Bambelweeny57/zxspectrum_issue3b/src/STPS/FERRANTI_ULA_6C001E-7.step

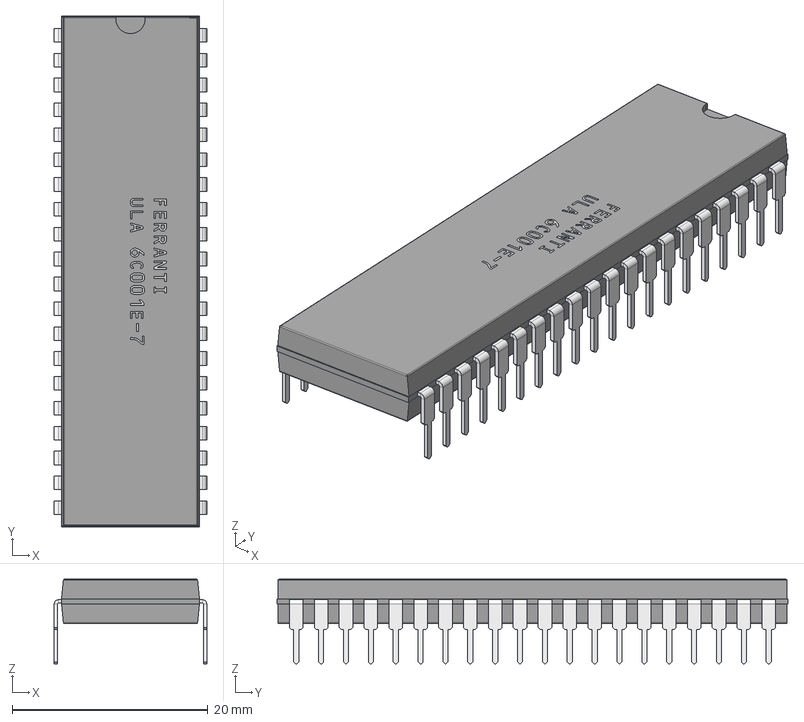
[picture p17: CAD file, 2026-09-03]
src/STPS/FERRANTI_ULA_6C001E-7.step
15.6 x 52.2 x 8.64 mm
Basic - DIP40 Wide v2
DIP Pin v2
DIP Pin v2(Mirror)
