Bambelweeny57/zxspectrum_issue3b/src/STPS/ROM HITACHI HN613128P.step

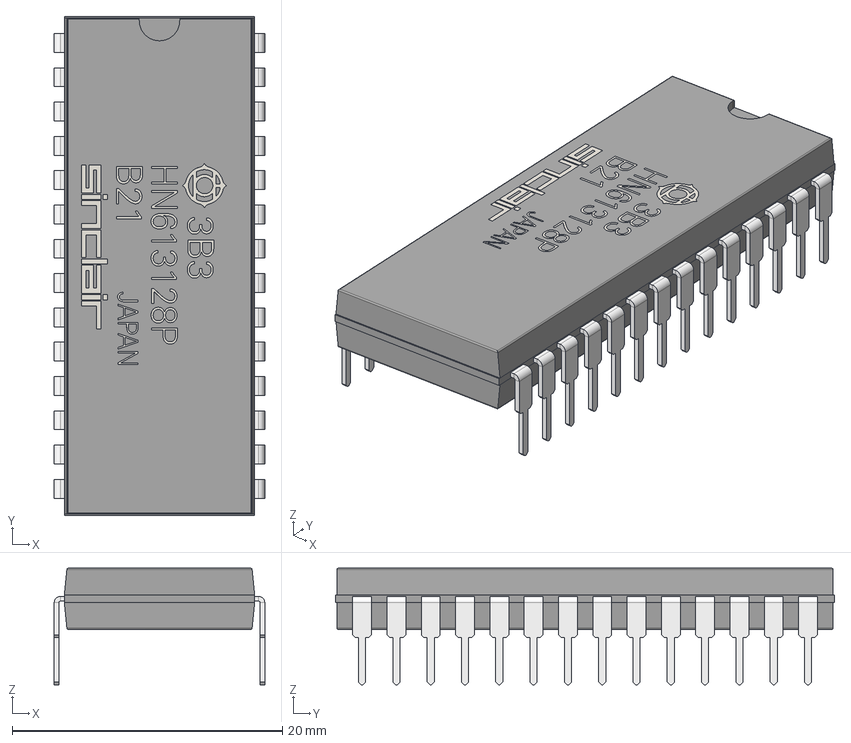
[picture p18: CAD file, 2026-09-03]
src/STPS/ROM HITACHI HN613128P.step
15.6 x 37.0 x 8.64 mm
Basic - DIP40 Wide v2
DIP Pin v2
DIP Pin v2(Mirror)
