Bambelweeny57/zxspectrum_issue3b/src/STPS/ZX Spectrum Speaker 40ohm.step

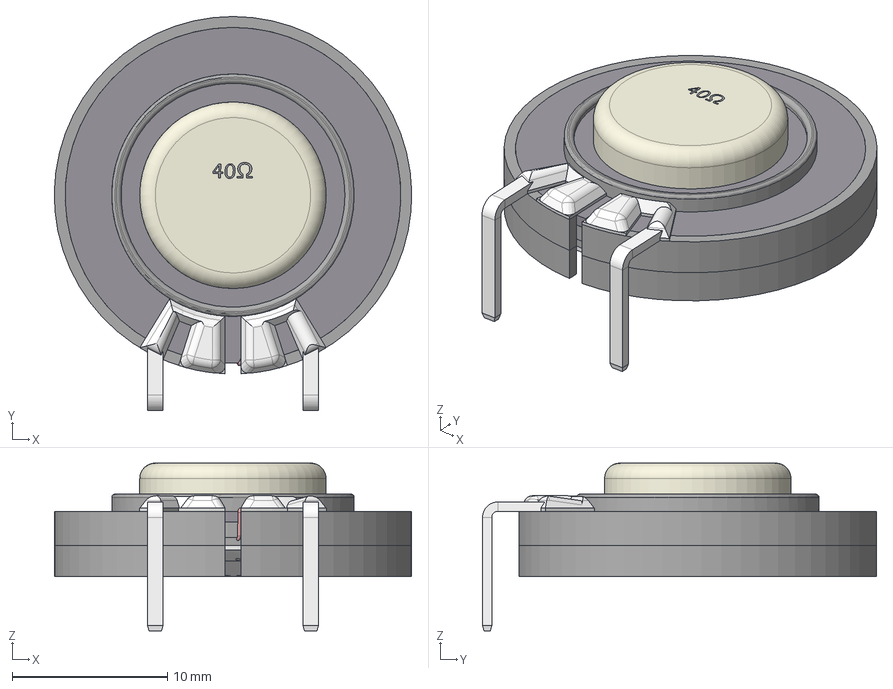
[picture p19: CAD file, 2026-09-01]
src/STPS/ZX Spectrum Speaker 40ohm.step
23.0 x 25.4 x 10.8 mm
Magnet
Plastic Cover
Board
CopperWire
Pins
