Bambelweeny57/zxspectrum_issue3b/src/STPS/COIL_L1.step

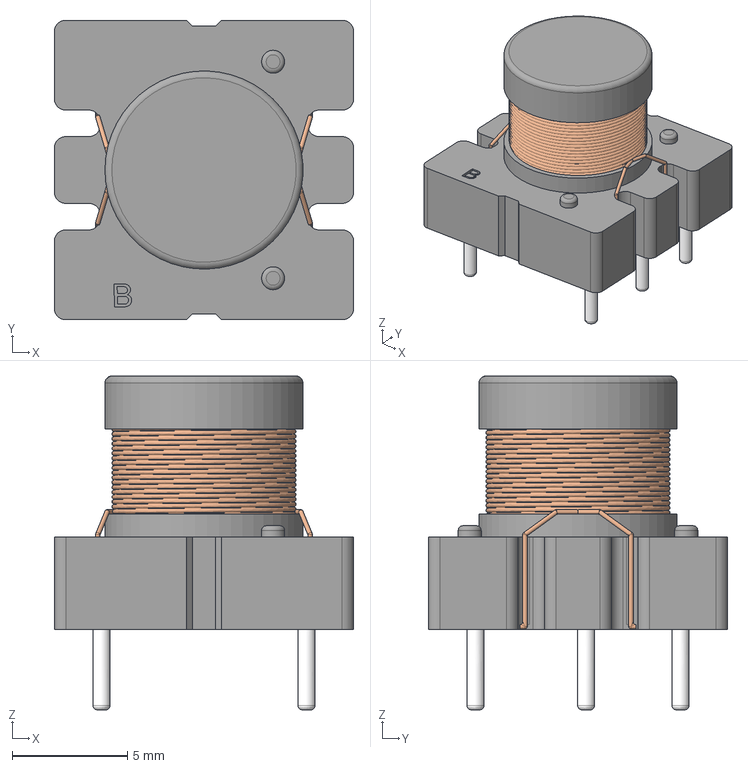
[picture p20: CAD file, 2026-09-01]
src/STPS/COIL_L1.step
13.0 x 13.0 x 14.5 mm
