Bambelweeny57/zxspectrum_issue3b/src/STPS/ZX Spectrum 48k Speaker.step

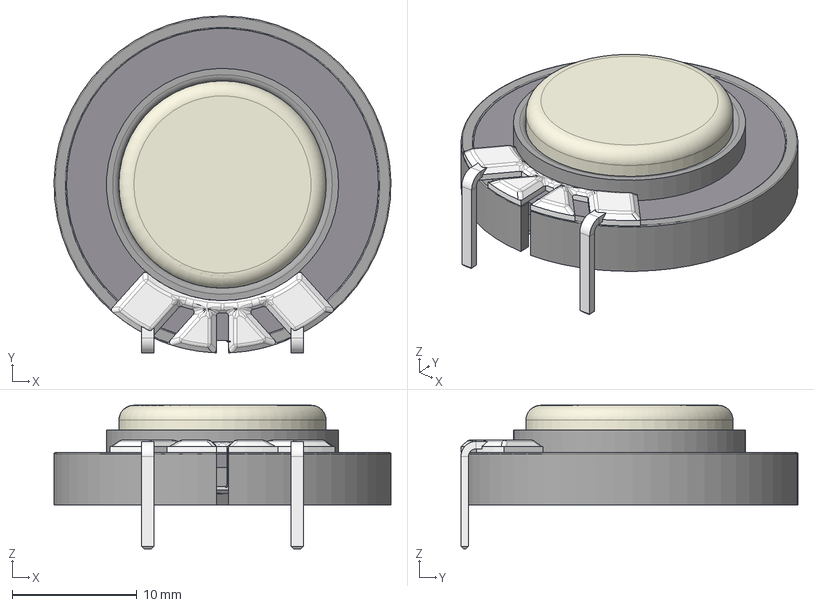
[picture p21: CAD file, 2026-09-01]
src/STPS/ZX Spectrum 48k Speaker.step
27.0 x 27.0 x 11.5 mm
Magnet
Soldering
pins
Plastic Film
Copper Wire
