Bambelweeny57/zxspectrum_issue3b/src/STPS/DIP-28_W15.24mm_Socket.step

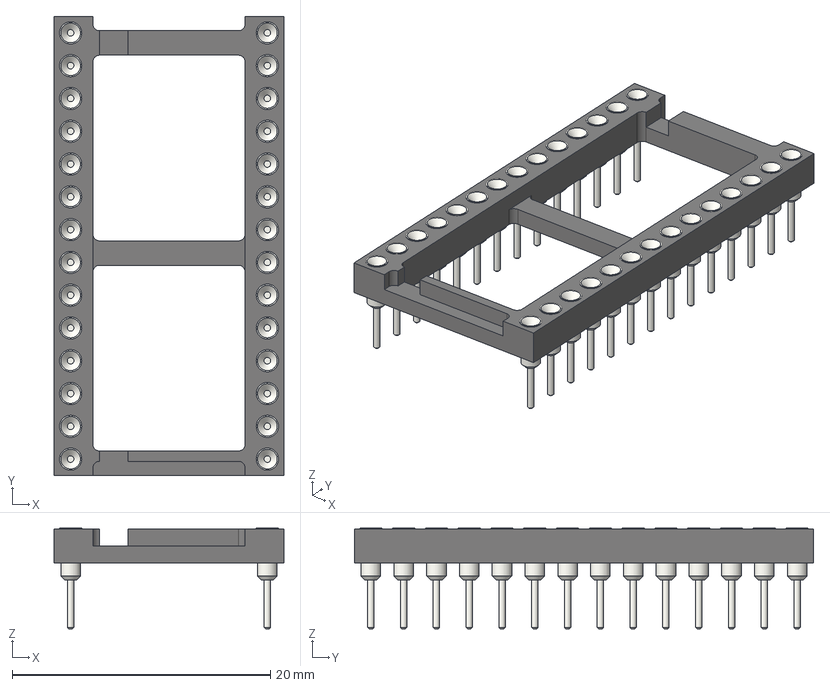
[picture p22: CAD file, 2026-08-31]
src/STPS/DIP-28_W15.24mm_Socket.step
17.8 x 35.6 x 7.79 mm
