Bambelweeny57/zxspectrum_issue3b/src/STPS/CP 13x5x0.5x20.32.STEP

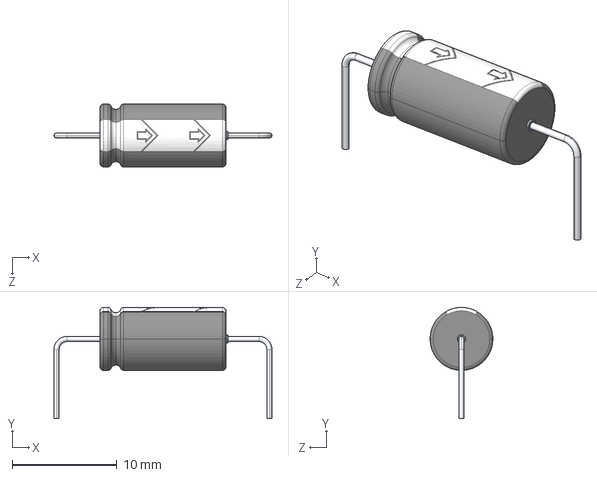
[picture p23: CAD file, 2026-08-31]
src/STPS/CP 13x5x0.5x20.32.STEP
20.8 x 10.6 x 6.00 mm
