Bambelweeny57/zxspectrum_issue3b/src/STPS/Resistor-0414-11.5x4.5x22.86.STEP

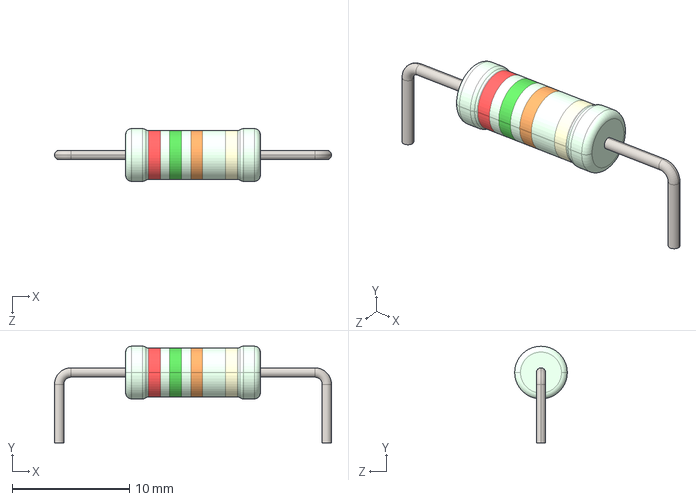
[picture p24: CAD file, 2026-08-31]
src/STPS/Resistor-0414-11.5x4.5x22.86.STEP
23.7 x 8.25 x 4.50 mm
