Bambelweeny57/zxspectrum_issue3b/src/STPS/DIP-24_W10.16mm.step

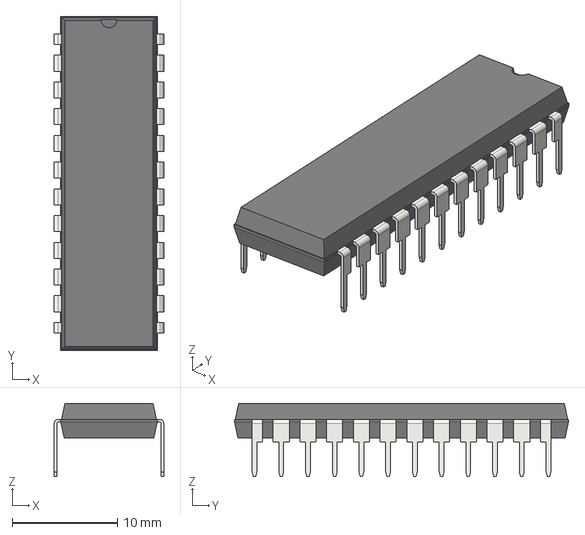
[picture p25: CAD file, 2026-08-31]
src/STPS/DIP-24_W10.16mm.step
10.4 x 31.8 x 6.98 mm
