Bambelweeny57/zxspectrum_issue3b/src/STPS/DIP-18_W7.62mm.step

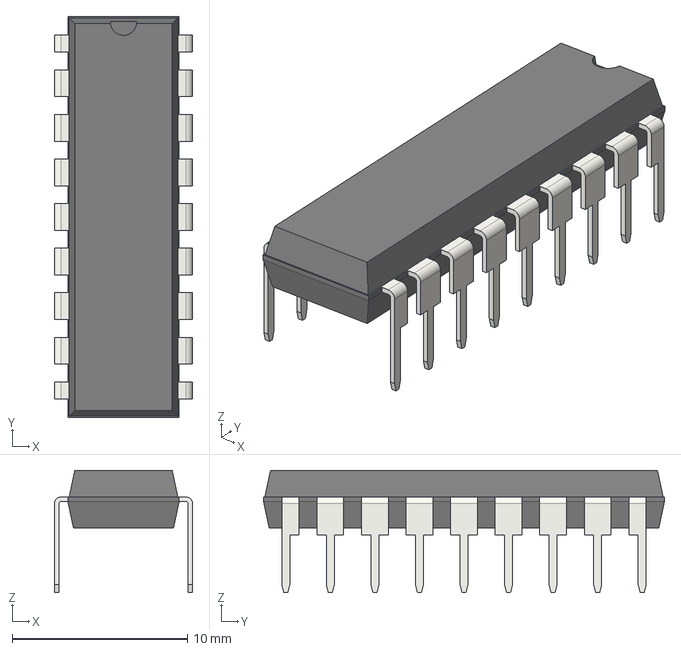
[picture p26: CAD file, 2026-08-31]
src/STPS/DIP-18_W7.62mm.step
7.87 x 22.9 x 6.98 mm
