Bambelweeny57/zxspectrum_issue3b/src/STPS/UM1233.step

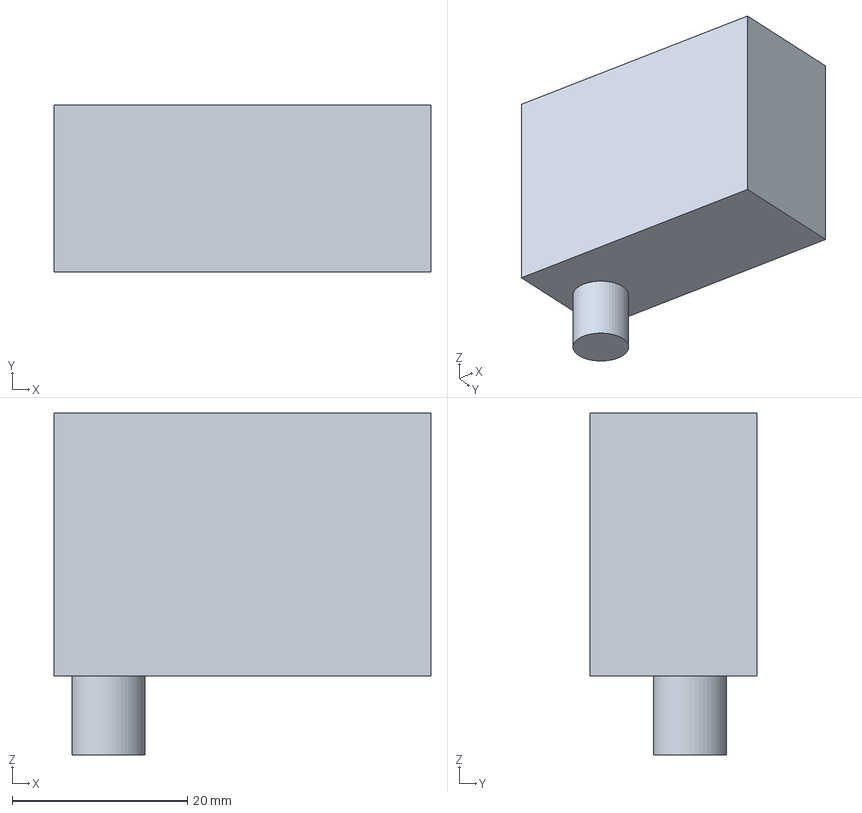
[picture p27: CAD file, 2026-08-31]
src/STPS/UM1233.step
43.0 x 19.0 x 39.0 mm
