Bambelweeny57/zxspectrum_issue3b/src/STPS/DIP-24_W10.16mm_Socket.step

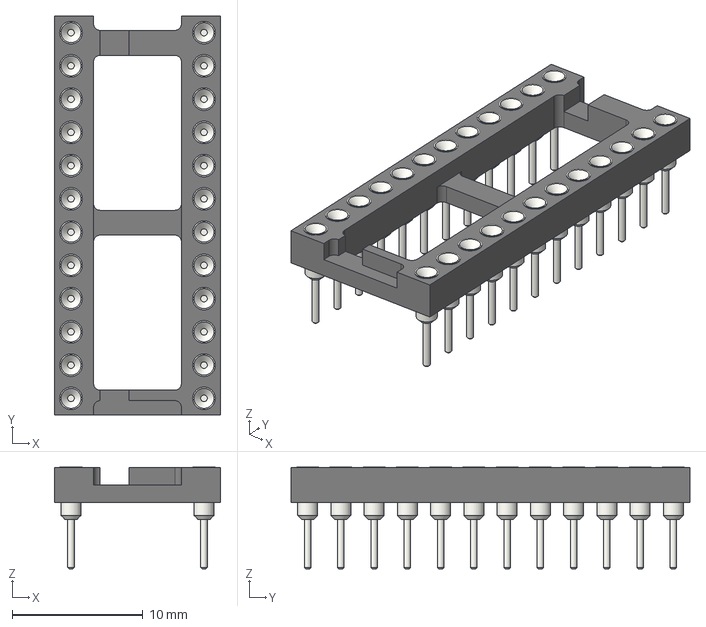
[picture p28: CAD file, 2026-08-31]
src/STPS/DIP-24_W10.16mm_Socket.step
12.7 x 30.5 x 7.79 mm
