Bambelweeny57/zxspectrum_issue3b/src/STPS/Transistor Kinked Lead.stp

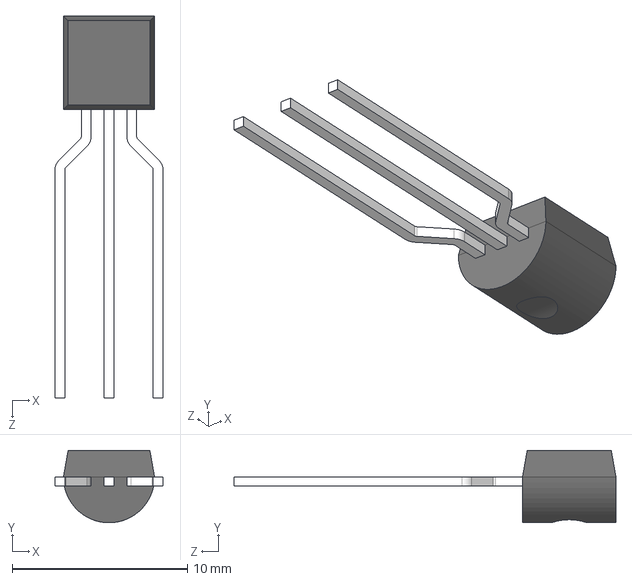
[picture p29: CAD file, 2026-08-31]
src/STPS/Transistor Kinked Lead.stp
6.16 x 4.13 x 21.8 mm
