Bambelweeny57/zxspectrum_issue3b/src/STPS/Capacitor Ceramic No Polarity axial 12.70.STEP

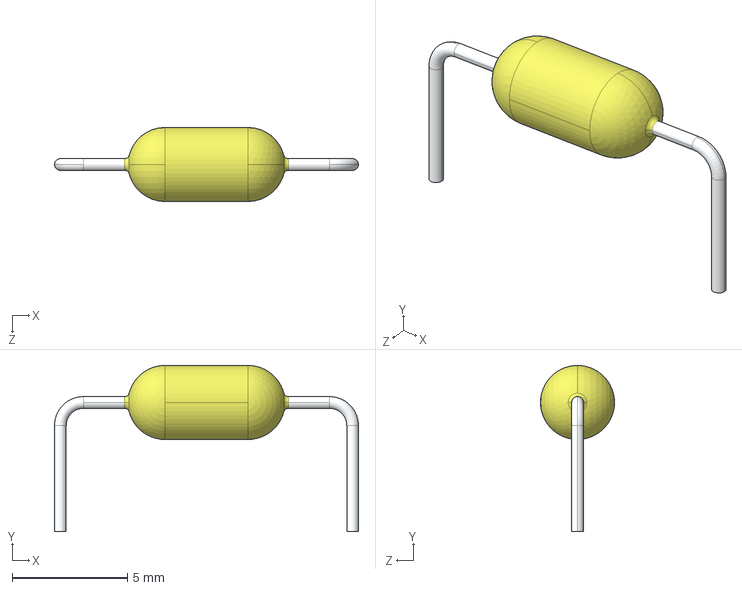
[picture p30: CAD file, 2026-08-31]
src/STPS/Capacitor Ceramic No Polarity axial 12.70.STEP
13.2 x 7.22 x 3.22 mm
