Bambelweeny57/zxspectrum_issue3b/src/STPS/22-02-3083.stp

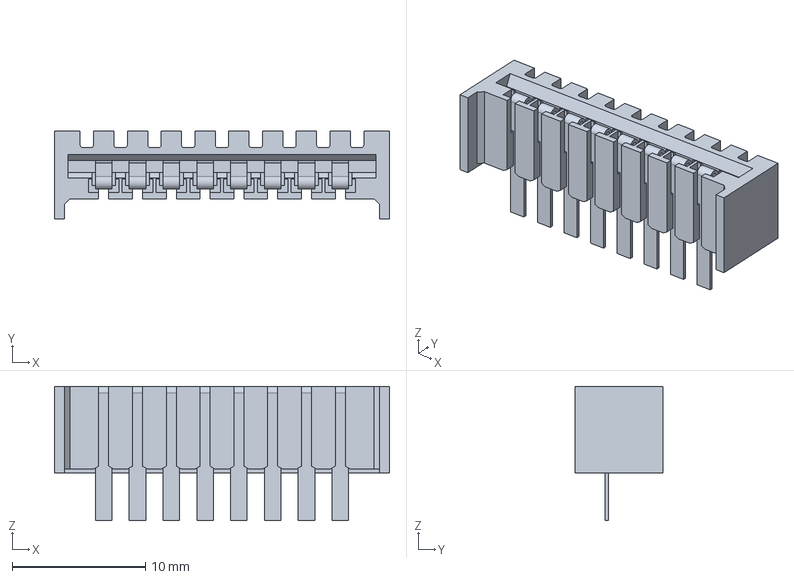
[picture p31: CAD file, 2026-08-31]
src/STPS/22-02-3083.stp
25.2 x 6.60 x 10.1 mm
