Bambelweeny57/zxspectrum_issue3b/src/STPS/DIP-18_W7.62mm_Socket.step

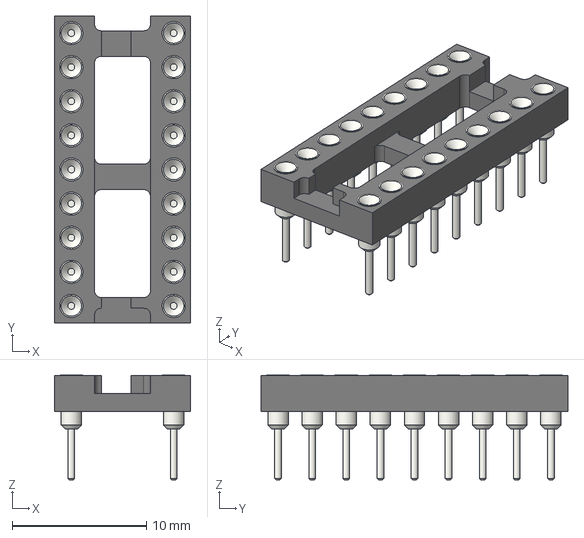
[picture p32: CAD file, 2026-08-31]
src/STPS/DIP-18_W7.62mm_Socket.step
10.2 x 22.9 x 7.79 mm
