Bambelweeny57/zxspectrum_issue3b/src/STPS/DO-35_3.90x1.90x0.60x12.70.STEP

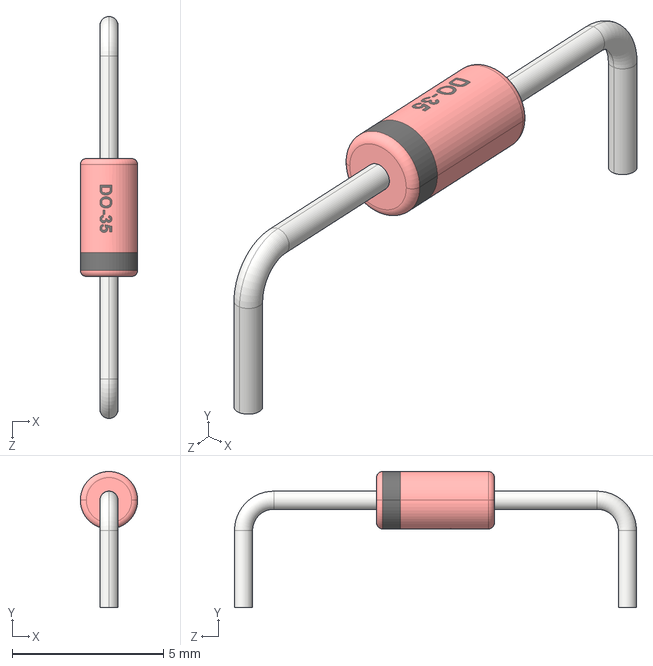
[picture p33: CAD file, 2026-08-31]
src/STPS/DO-35_3.90x1.90x0.60x12.70.STEP
1.90 x 4.50 x 13.3 mm
