Bambelweeny57/zxspectrum_issue3b/src/STPS/TO220 Horizontal - Bent Leads.STEP

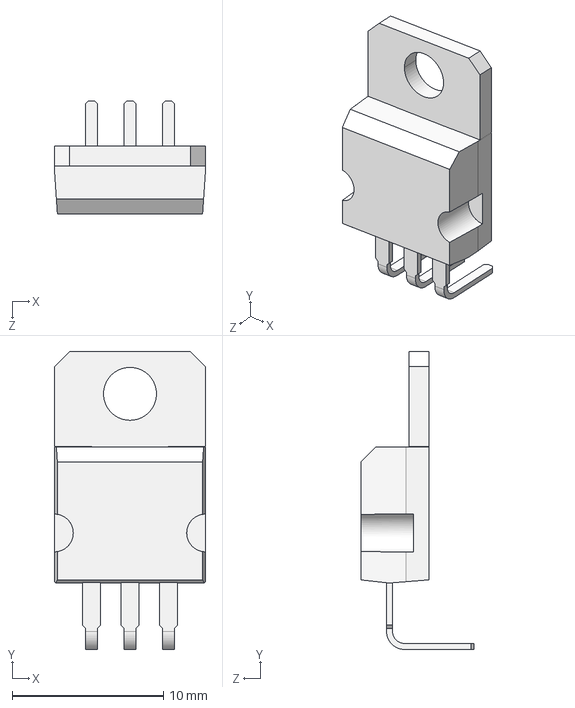
[picture p34: CAD file, 2026-08-31]
src/STPS/TO220 Horizontal - Bent Leads.STEP
10.0 x 19.7 x 7.50 mm
