Bambelweeny57/zxspectrum_issue3b/src/STPS/Crystal-Low.stp

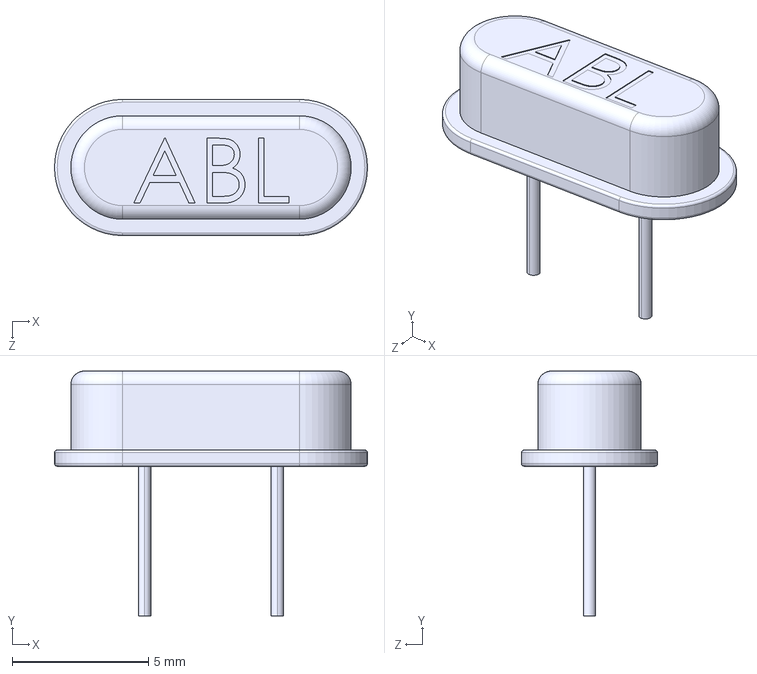
[picture p37: CAD file, 2026-08-31]
src/STPS/Crystal-Low.stp
11.5 x 9.00 x 5.00 mm
