Bambelweeny57/zxspectrum_issue3b/src/STPS/Resistor-0207-6.3x2.4x12.40.STEP

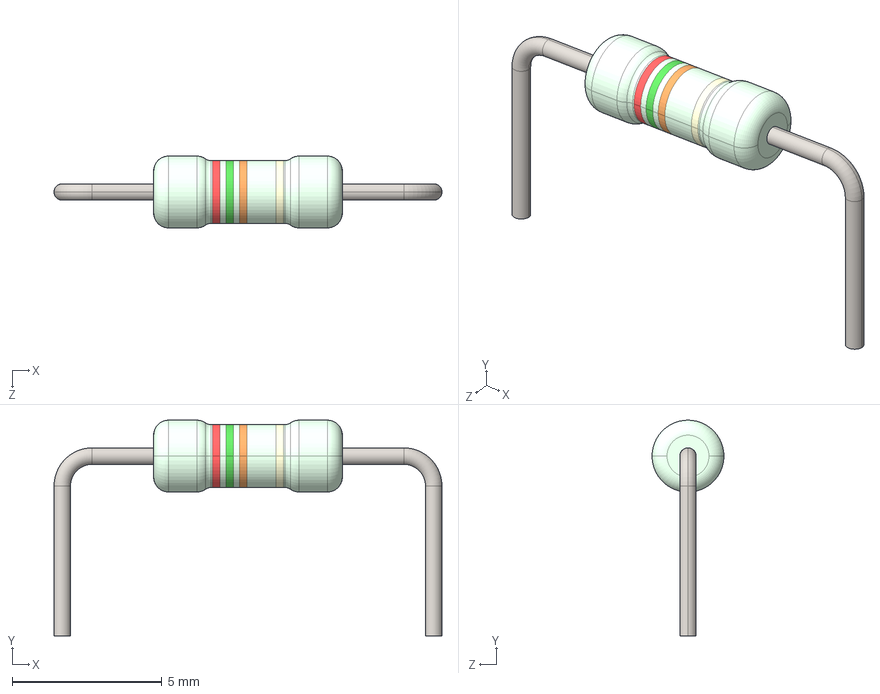
[picture p39: CAD file, 2026-08-31]
src/STPS/Resistor-0207-6.3x2.4x12.40.STEP
13.0 x 7.20 x 2.40 mm
