Bambelweeny57/zxspectrum_issue3b/src/STPS/Speaker SM230332-2.stp

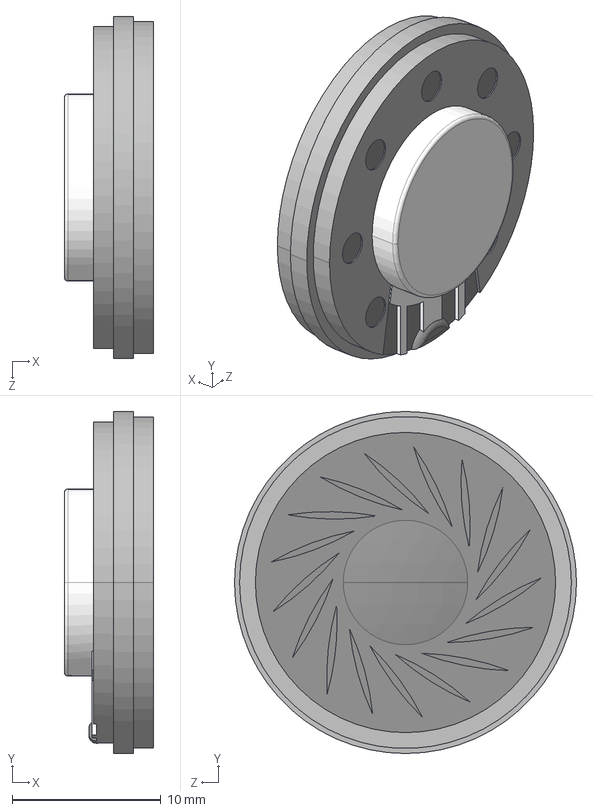
[picture p40: CAD file, 2026-08-31]
src/STPS/Speaker SM230332-2.stp
6.00 x 23.0 x 23.0 mm
