Bambelweeny57/zxspectrum_issue3b/src/STPS/WireLink 7.62mm 1430-3.STEP

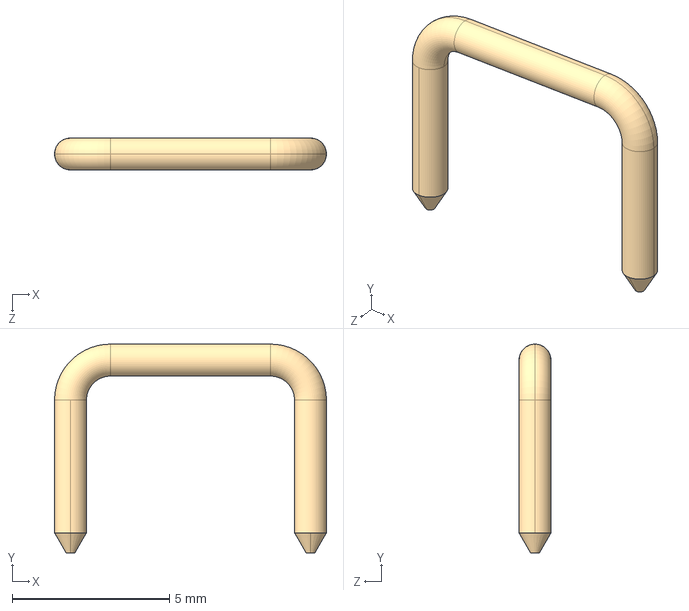
[picture p41: CAD file, 2026-08-31]
src/STPS/WireLink 7.62mm 1430-3.STEP
8.64 x 6.63 x 1.02 mm
