Bambelweeny57/zxspectrum_issue3b/src/STPS/DIP-40_W15.24mm_Socket.step

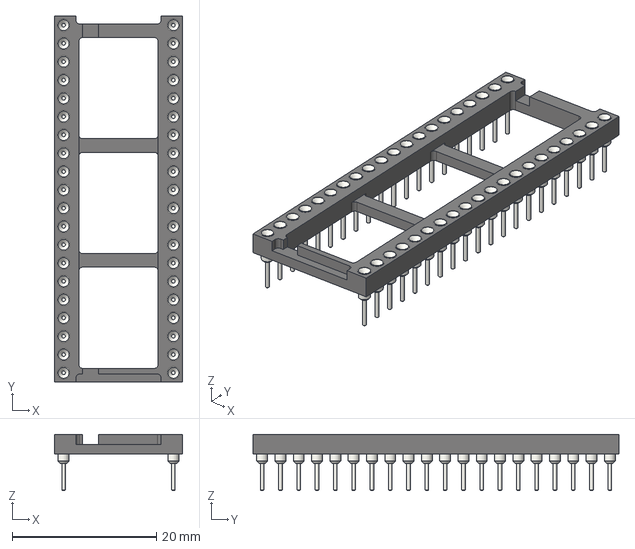
[picture p43: CAD file, 2026-08-31]
src/STPS/DIP-40_W15.24mm_Socket.step
17.8 x 50.8 x 7.79 mm
