Bambelweeny57/zxspectrum_issue3b/src/STPS/DIP-28_W15.24mm.step

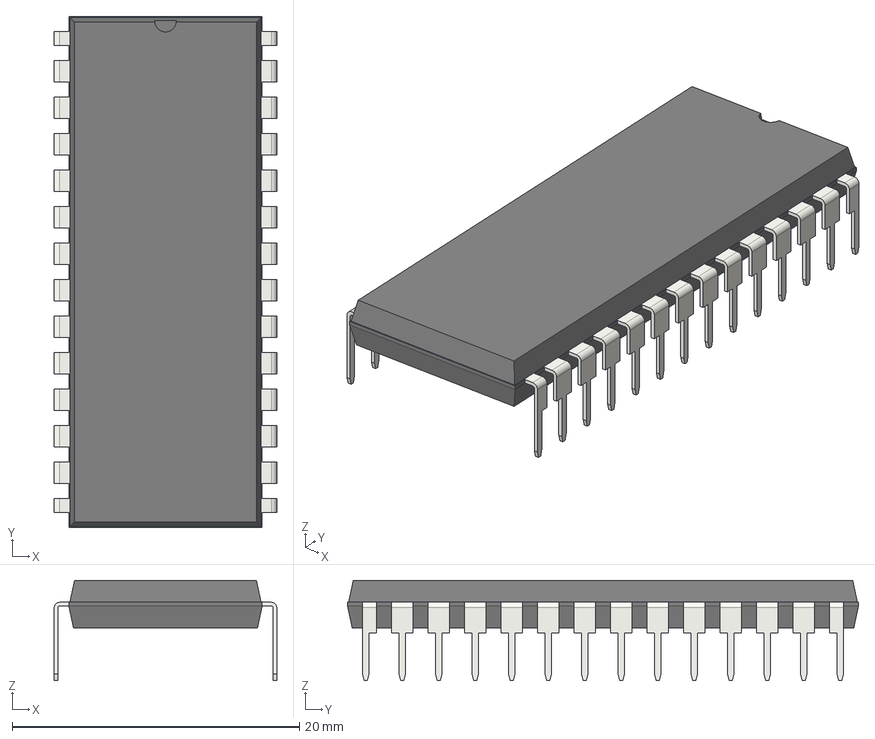
[picture p44: CAD file, 2026-08-31]
src/STPS/DIP-28_W15.24mm.step
15.5 x 35.6 x 6.98 mm
