Bambelweeny57/zxspectrum_issue3b/src/STPS/Crystal-HC18-U RA.STEP

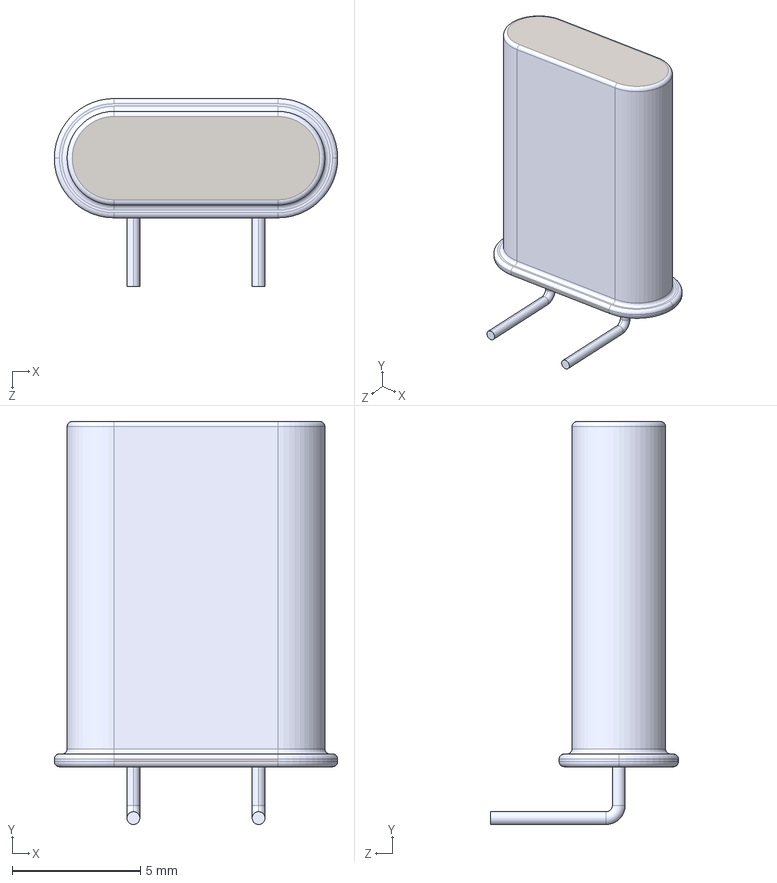
[picture p45: CAD file, 2026-08-31]
src/STPS/Crystal-HC18-U RA.STEP
11.1 x 15.7 x 7.32 mm
