Bambelweeny57/zxspectrum_issue3b/src/STPS/DIP-14_W7.62mm.step

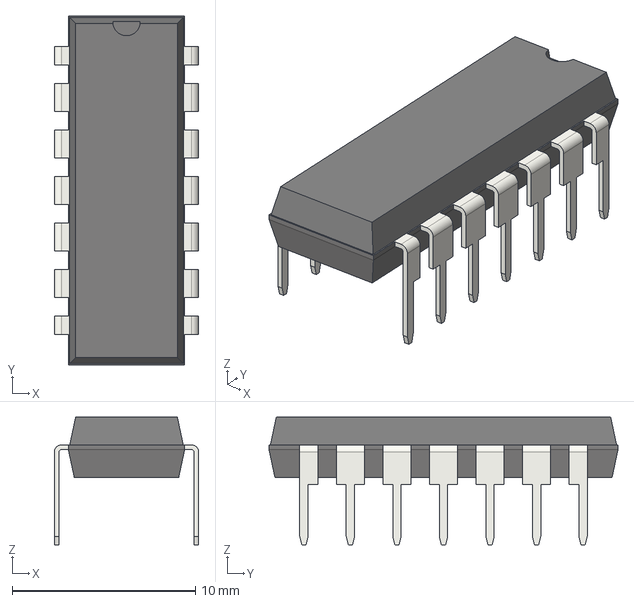
[picture p46: CAD file, 2026-08-31]
src/STPS/DIP-14_W7.62mm.step
7.87 x 19.1 x 6.98 mm
