Bambelweeny57/zxspectrum_issue3b/src/STPS/DC Power Connector FC68148_20DC10A_202.1mm.STP

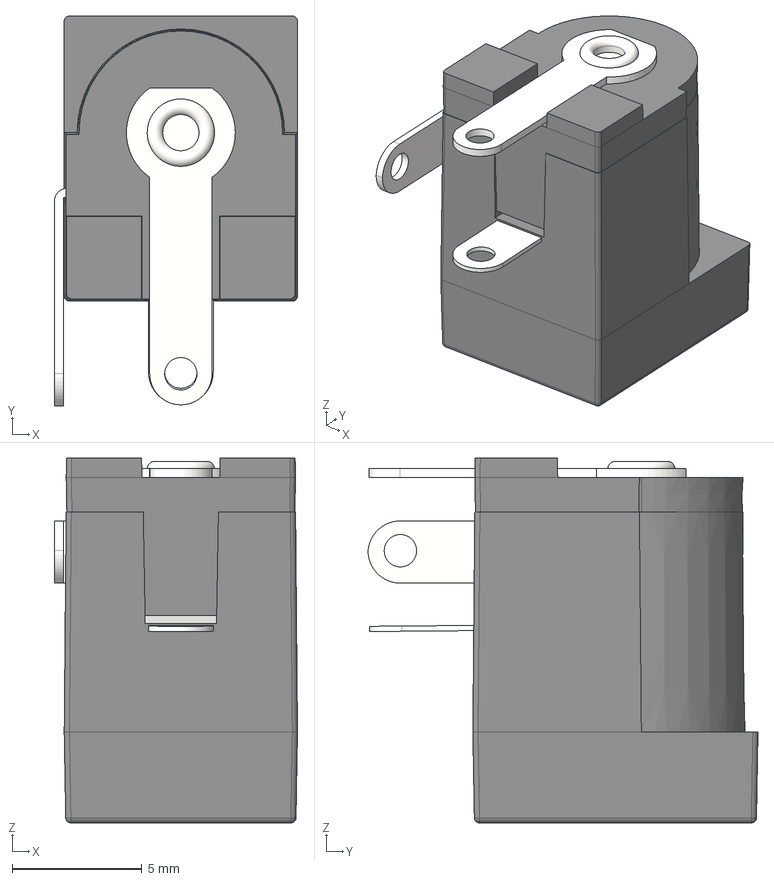
[picture p47: CAD file, 2026-08-31]
src/STPS/DC Power Connector FC68148_20DC10A_202.1mm.STP
9.37 x 15.0 x 14.1 mm
