Bambelweeny57/zxspectrum_issue3b/src/STPS/13.34x13.34 Bobin.STEP

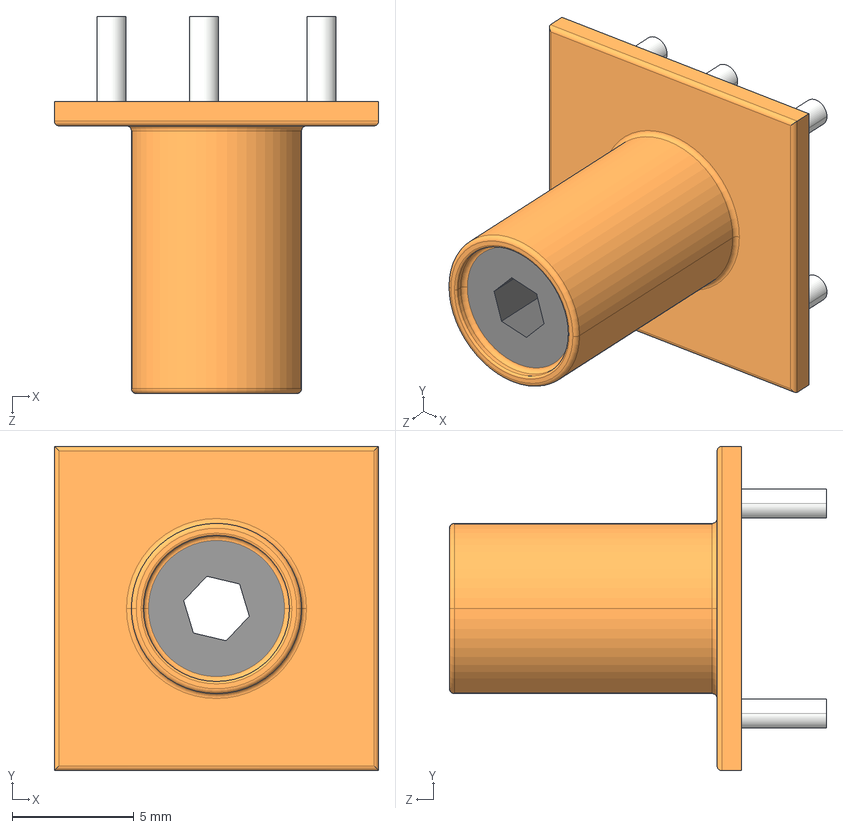
[picture p48: CAD file, 2026-08-31]
src/STPS/13.34x13.34 Bobin.STEP
13.3 x 13.3 x 15.5 mm
