Bambelweeny57/zxspectrum_issue3b/src/STPS/TO-92S_Normal_LF42_rev1.0.STEP

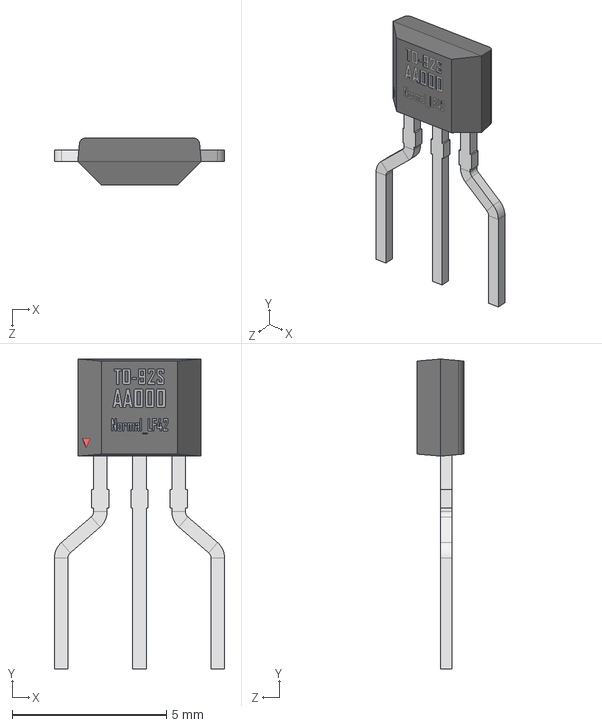
[picture p49: CAD file, 2026-08-31]
src/STPS/TO-92S_Normal_LF42_rev1.0.STEP
5.52 x 10.1 x 1.52 mm
