Bambelweeny57/zxspectrum_issue3b/src/STPS/FCR1281 S6A 6mm.stp

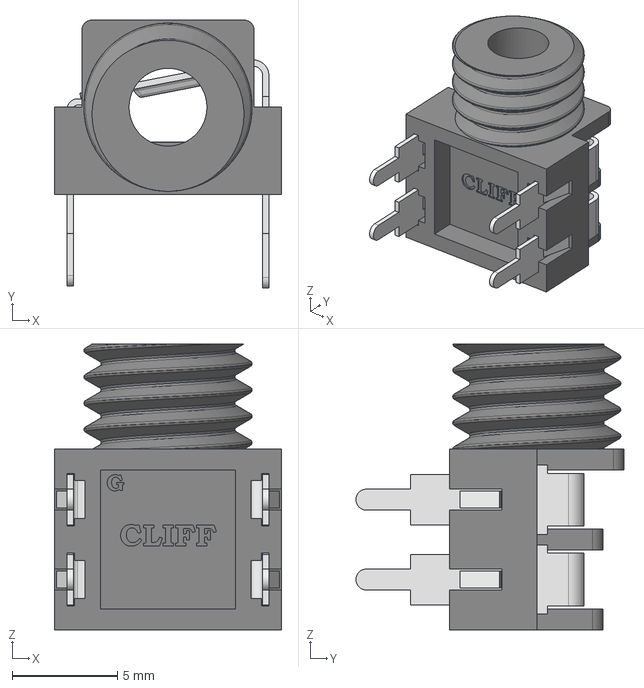
[picture p50: CAD file, 2026-08-31]
src/STPS/FCR1281 S6A 6mm.stp
10.8 x 12.8 x 13.6 mm
