Bambelweeny57/zxspectrum_issue3b/src/STPS/DIP-40_W15.24mm.step

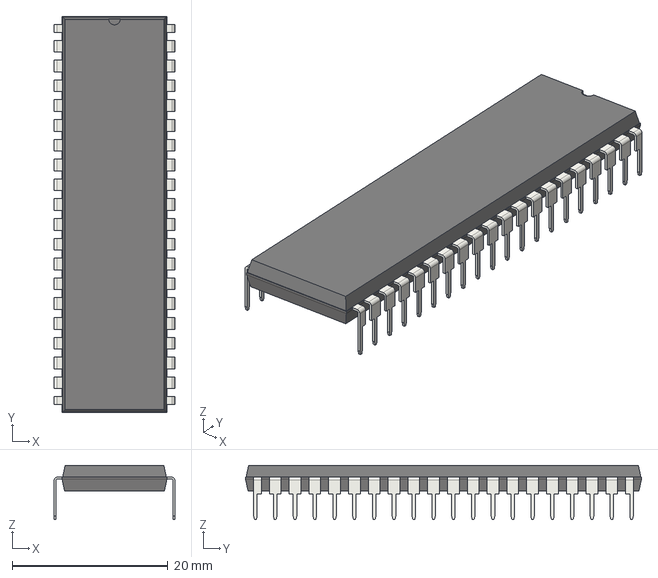
[picture p51: CAD file, 2026-08-31]
src/STPS/DIP-40_W15.24mm.step
15.5 x 50.8 x 6.98 mm
