Bambelweeny57/zxspectrum_issue3b/src/STPS/22-02-3053.stp

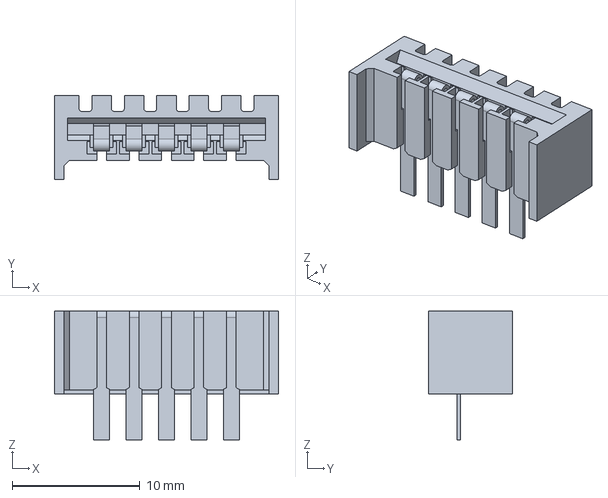
[picture p52: CAD file, 2026-08-31]
src/STPS/22-02-3053.stp
17.6 x 6.60 x 10.1 mm
