Bambelweeny57/zxspectrum_issue3b/src/STPS/RF MOD Astec UM1233 E36.step

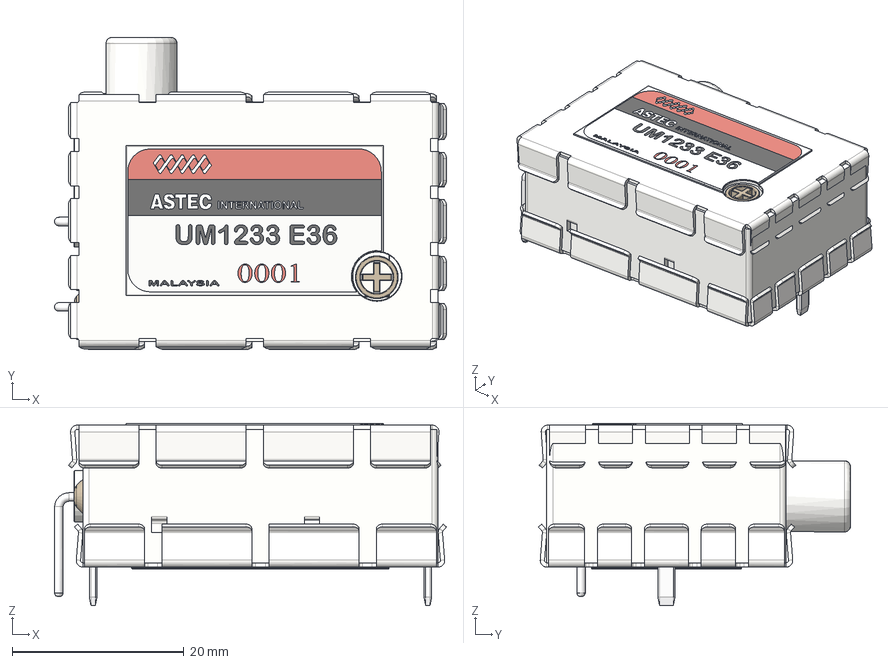
[picture p53: CAD file, 2026-08-30]
src/STPS/RF MOD Astec UM1233 E36.step
45.7 x 36.4 x 21.3 mm
Metal Body
Lid Bottom
Lid Top
