Bambelweeny57/zxspectrum_issue3b/src/STPS/CONN-TH_8P-P2.54_520315-8.step

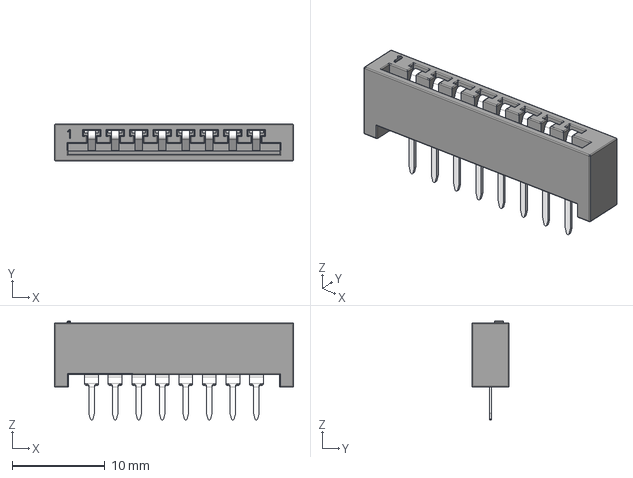
[picture p54: CAD file, 2026-08-30]
src/STPS/CONN-TH_8P-P2.54_520315-8.step
25.8 x 4.00 x 10.7 mm
Pins
Connector Body
