Bambelweeny57/zxspectrum_issue3b/src/STPS/CONN-TH_5P-P2.54_520315-5.step

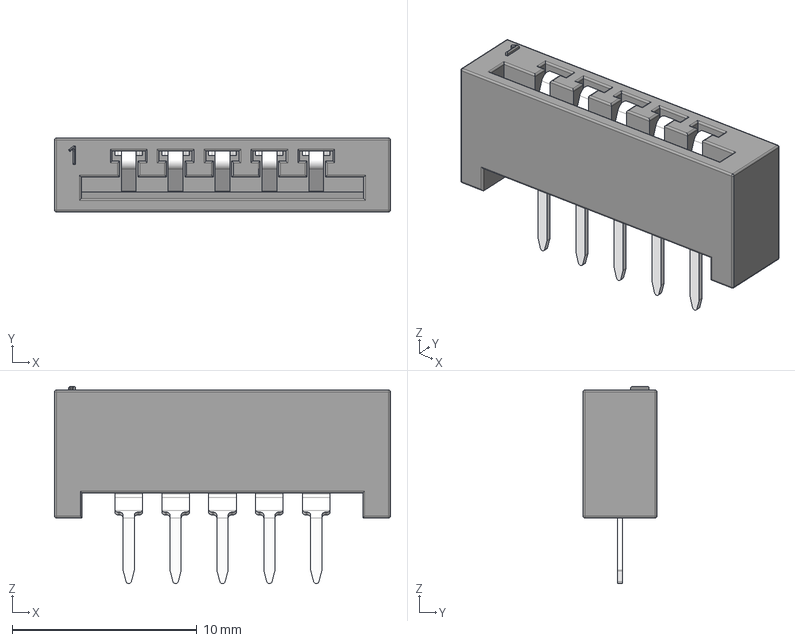
[picture p55: CAD file, 2026-08-30]
src/STPS/CONN-TH_5P-P2.54_520315-5.step
18.2 x 4.00 x 10.7 mm
Pins
Connector Body
