Bambelweeny57/zxspectrum_issue3b/src/STPS/AUDIO_JACK_3PIN.step

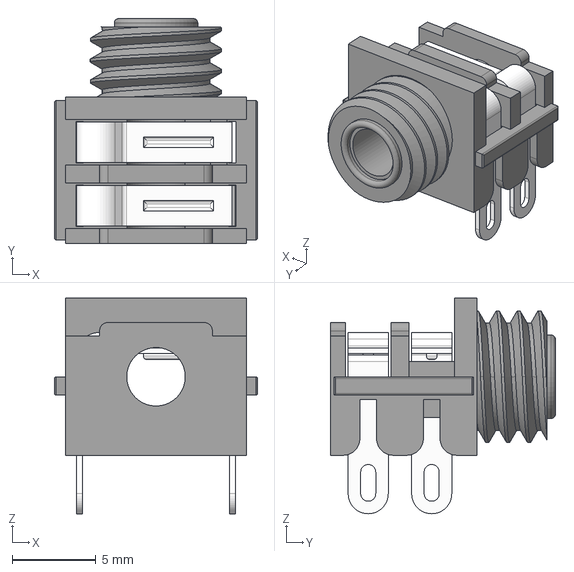
[picture p56: CAD file, 2026-08-30]
src/STPS/AUDIO_JACK_3PIN.step
12.2 x 13.4 x 12.9 mm
Pins
Plastic Body
